Horizon489732/E.A.R.L._Bot/Design Diagrams/class.png

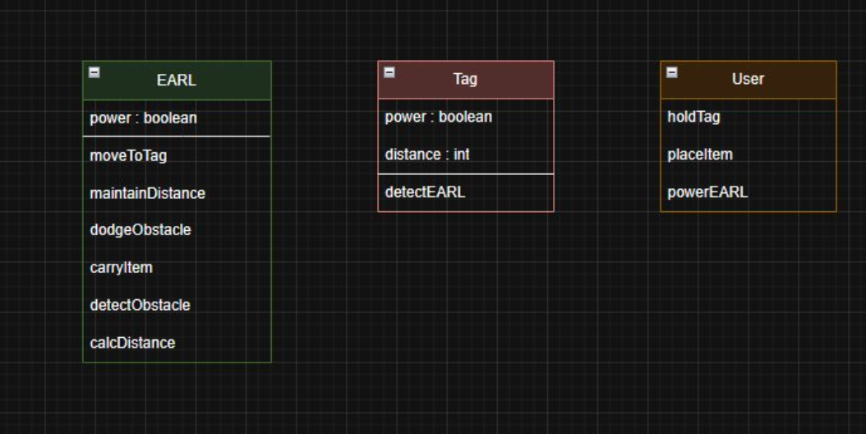
Design Diagrams/class.png
