Horizon489732/E.A.R.L._Bot/Design Diagrams/Sequence_Diagram.png

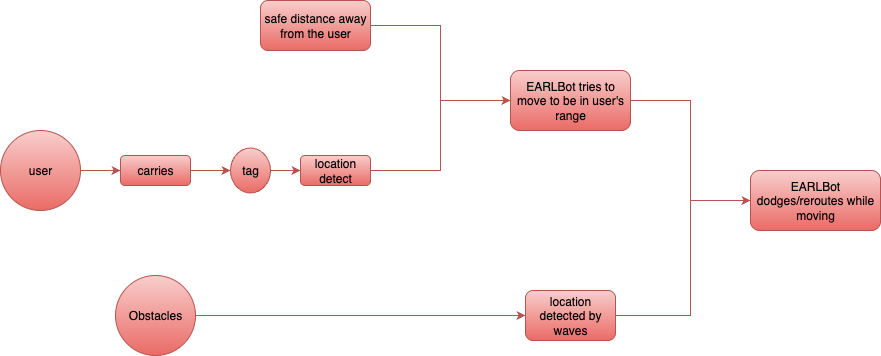
Design Diagrams/Sequence_Diagram.png
