Horizon489732/E.A.R.L._Bot/Design Diagrams/UI Mockups/Screenshot 2025-10-05 at 12.28.07 AM.png

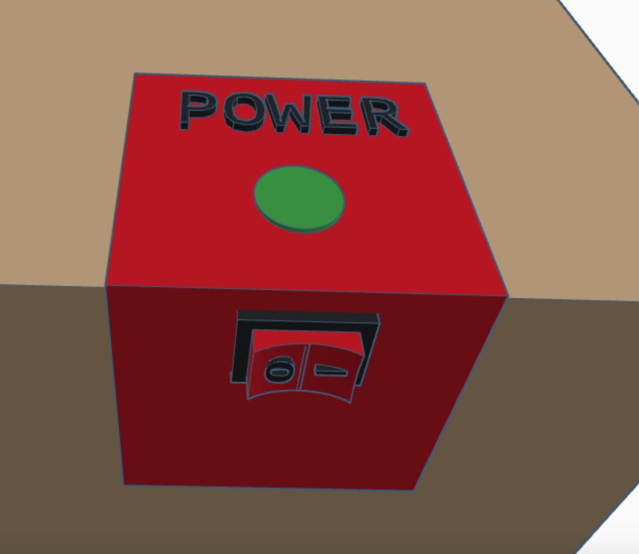
Design Diagrams/UI Mockups/Screenshot 2025-10-05 at 12.28.07 AM.png
