Horizon489732/E.A.R.L._Bot/Documentation/IMG_0232.jpeg

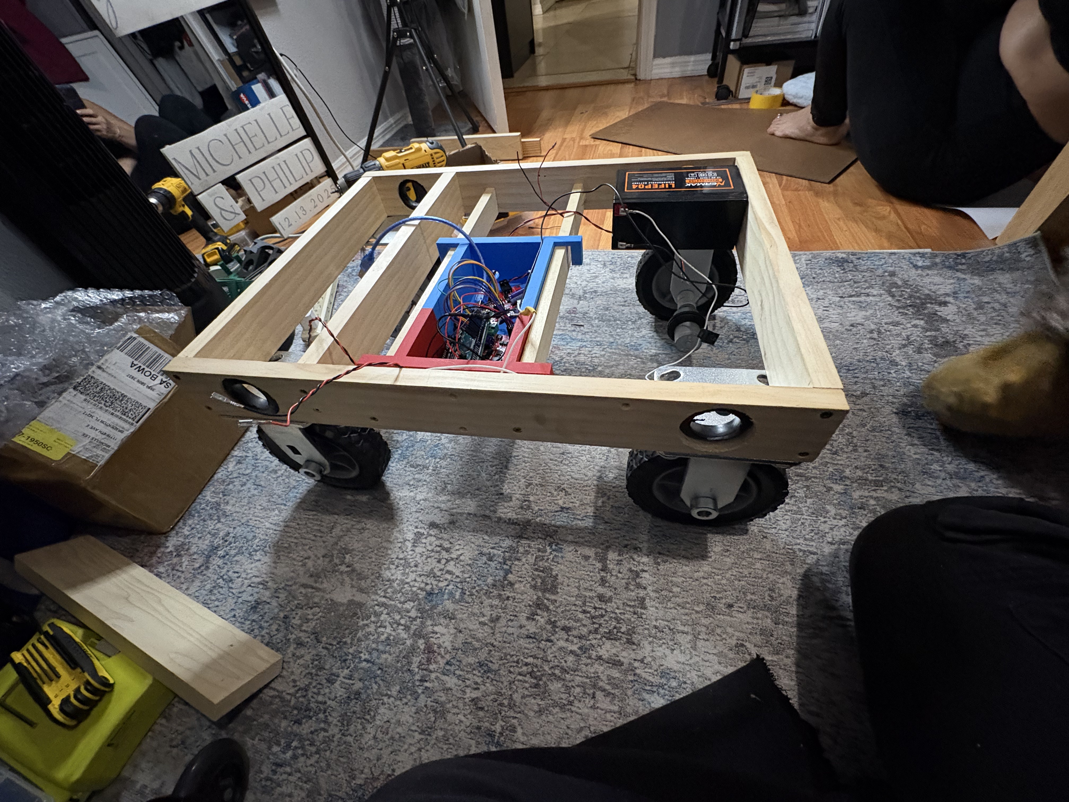
Documentation/IMG_0232.jpeg
