Horizon489732/E.A.R.L._Bot/Documentation/IMG_0437.JPG

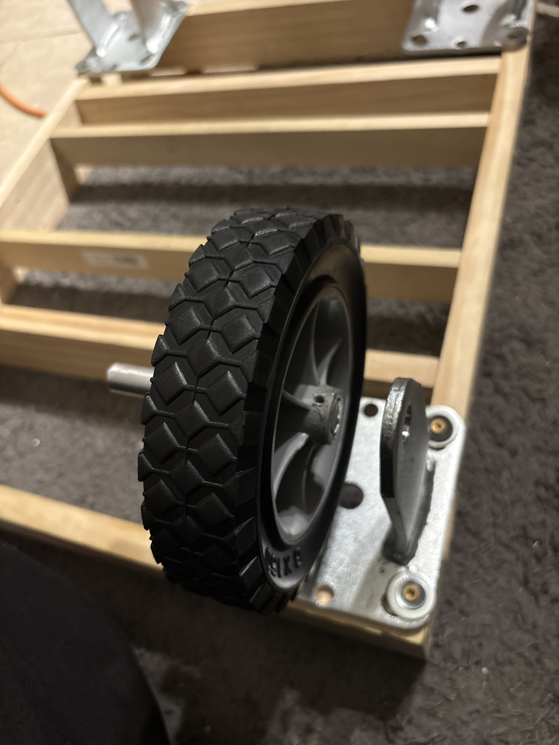
Documentation/IMG_0437.JPG
